OSHE-Github/Open-Source-Modular-Controller/Hardware/Module STLs/OSMC_Module_Joystick_Bottom.stl

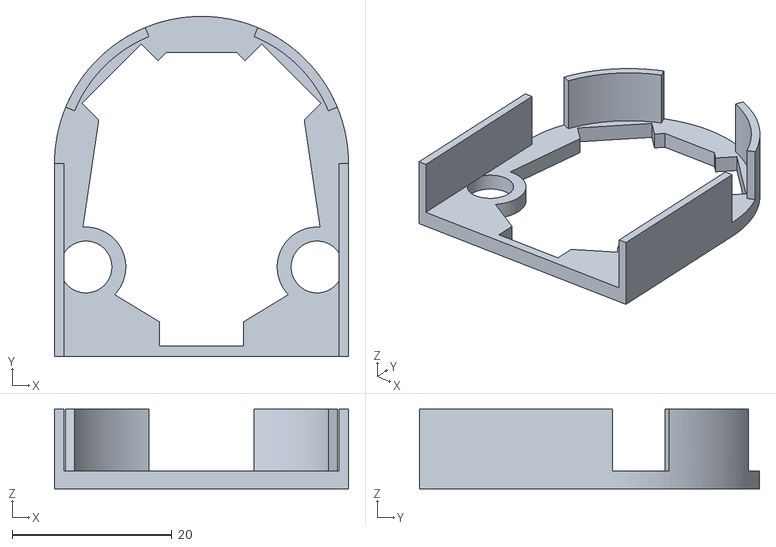
[picture p47: CAD file, 2026-04-23]
Hardware/Module STLs/OSMC_Module_Joystick_Bottom.stl
36.8 x 42.6 x 10.0
