OSHE-Github/Open-Source-Modular-Controller/Hardware/Module STLs/OSMC_Module_Buttons_Top.stl

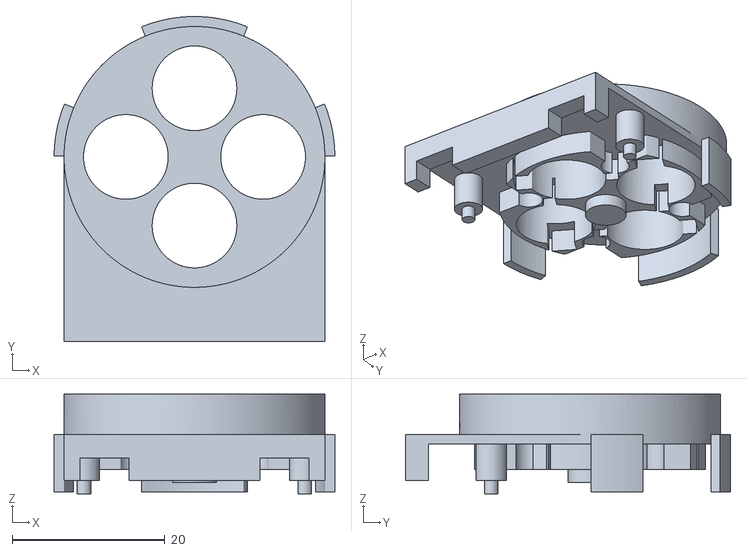
[picture p48: CAD file, 2026-04-23]
Hardware/Module STLs/OSMC_Module_Buttons_Top.stl
36.8 x 42.6 x 13.1
