OSHE-Github/Open-Source-Modular-Controller/Hardware/Module STLs/OSMC_Module_Master_Button.stl

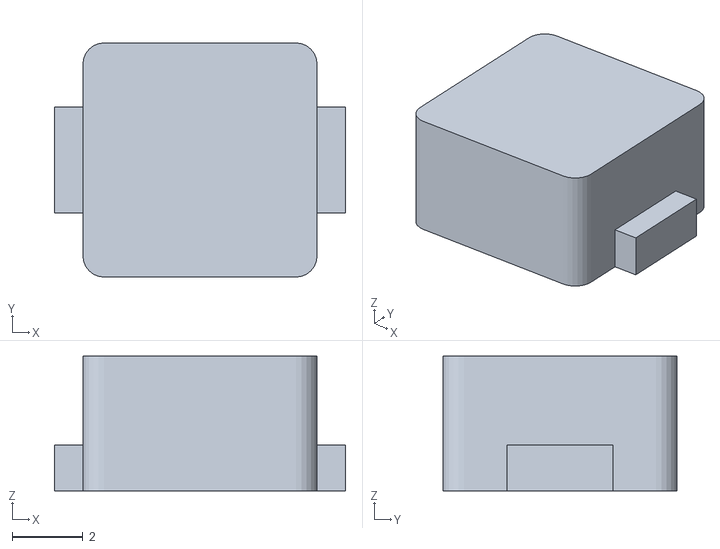
[picture p49: CAD file, 2026-04-23]
Hardware/Module STLs/OSMC_Module_Master_Button.stl
8.20 x 6.60 x 3.80
