OSHE-Github/Open-Source-Modular-Controller/Hardware/Module STLs/OSMC_Module_Buttons_Button.stl

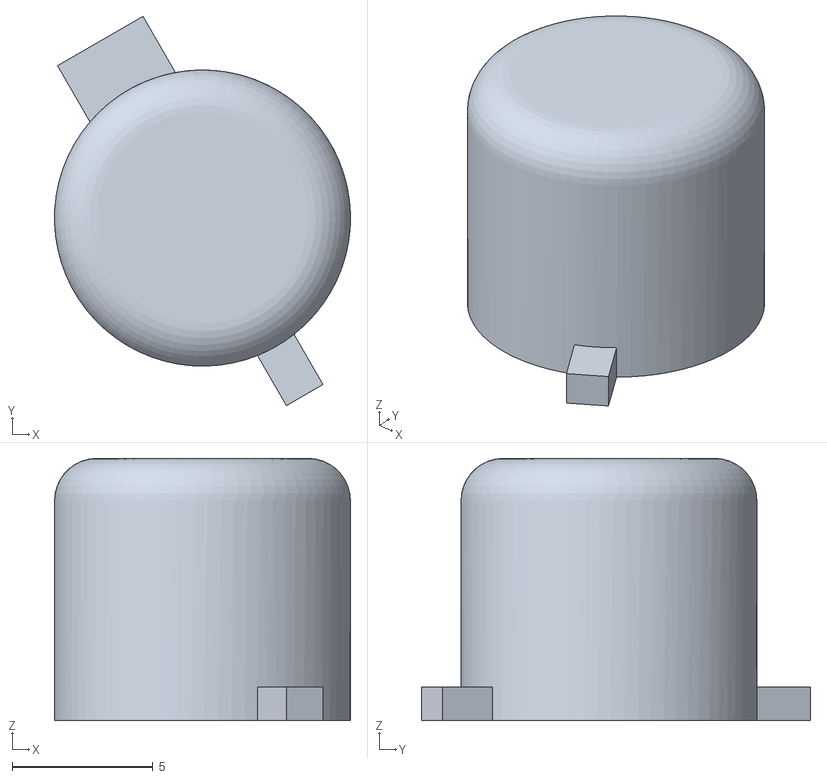
[picture p50: CAD file, 2026-04-23]
Hardware/Module STLs/OSMC_Module_Buttons_Button.stl
10.5 x 13.8 x 9.30
