OSHE-Github/Open-Source-Modular-Controller/Hardware/Module STLs/OSMC_Module_Master_Top.stl

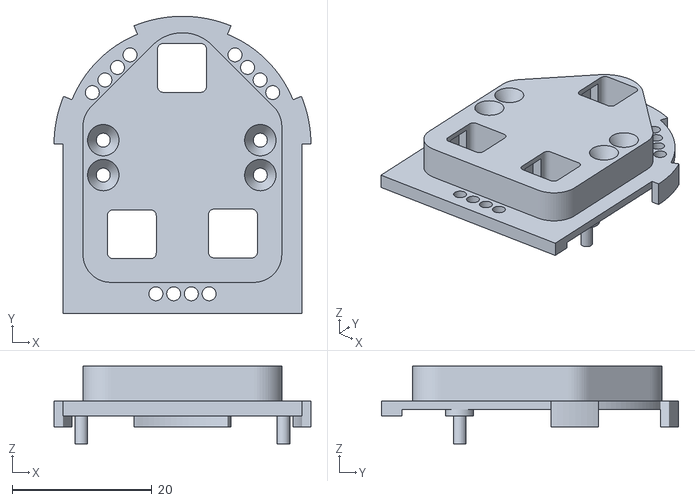
[picture p52: CAD file, 2026-04-23]
Hardware/Module STLs/OSMC_Module_Master_Top.stl
36.8 x 42.6 x 11.1
