OSHE-Github/Open-Source-Modular-Controller/Hardware/PCBs/module/OSMC_Module_Generic_Receiver/OSMC_Module_Generic_Receiver.kicad_pcb

## KiCad design Hardware/PCBs/module/OSMC_Module_Generic_Receiver/OSMC_Module_Generic_Receiver.kicad_pcb (2026-04-23)

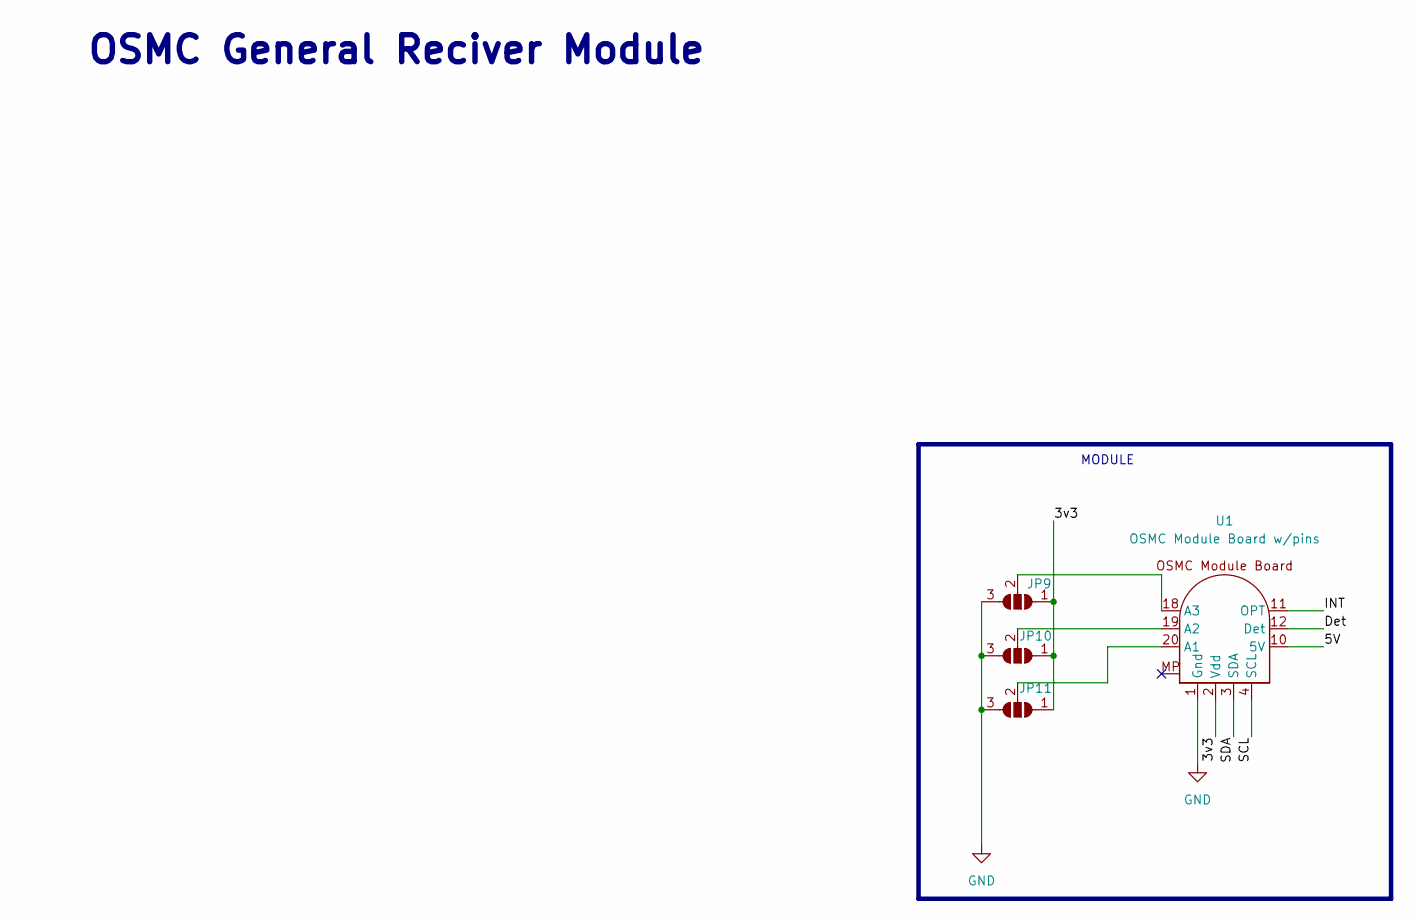
[picture p68: schematic OSMC_Module_Generic_Receiver.kicad_sch, OSMC_Module_Buttons]

Parts:
JP9, JP10, JP11: SolderJumper_3_Open; SolderJumper-3_P1.3mm_Open_Pad1.0x1.5mm
U1: OSMC Module Board w/pins; Module standard pin large

Connections:
/3v3: JP9.1 (A), JP10.1 (A), JP11.1 (A), U1.2 (Vdd), U1.6 (Vdd)
/5V: U1.10 (5V), U1.15 (5V)
/Det: U1.12 (Det), U1.13 (Int)
/INT: U1.11 (OPT), U1.14 (OPT)
/SCL: U1.4 (SCL), U1.8 (SCL)
/SDA: U1.3 (SDA), U1.7 (SDA)
GND: JP9.3 (B), JP10.3 (B), JP11.3 (B), U1.1 (Gnd), U1.5 (Gnd), U1.9 (Gnd), U1.16 (GND)
unnamed: JP9.2 (C), U1.18 (A3)
unnamed: JP10.2 (C), U1.19 (A2)
unnamed: JP11.2 (C), U1.20 (A1)

Notes on the sheet:
OSMC General Reciver Module
MODULE

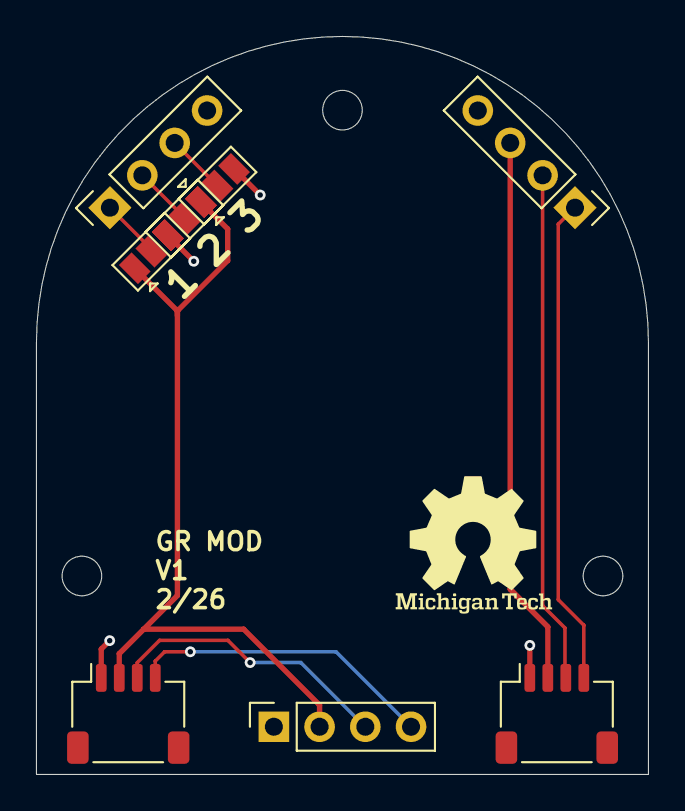
[picture p69: board OSMC_Module_Generic_Receiver.kicad_pcb from above]

Board: 2 copper layers, 34.0 x 41.0 mm, 4 parts (0 on the bottom side), 10 nets.
